gavinlyonsrepo/Cap_meter_arduino/docs/eagle/cap_meter.sch

## EAGLE design docs/eagle/cap_meter.sch (2019-02-24)

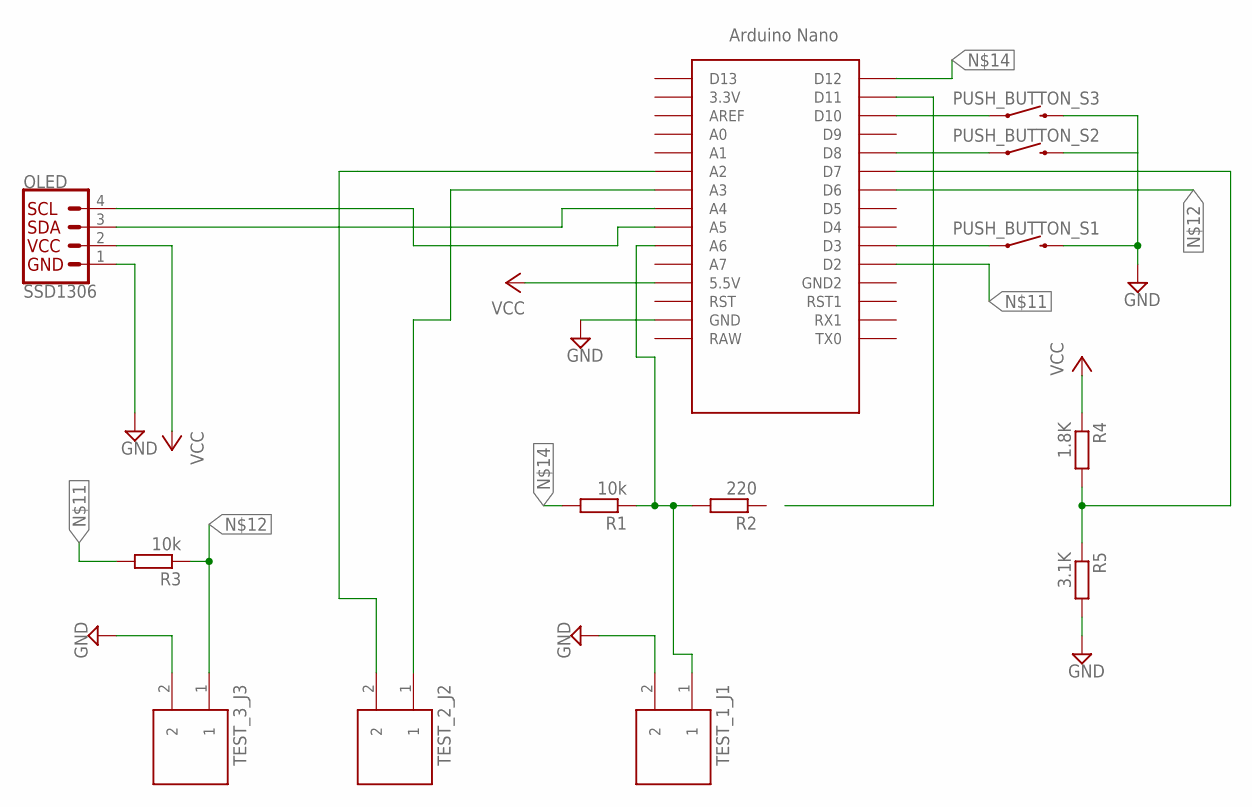
[picture p8: schematic cap_meter.sch]

Parts:
OLED: SSD1306; 1X04
PUSH_BUTTON_S1, PUSH_BUTTON_S2, PUSH_BUTTON_S3: MOMENTARY-SWITCH-SPST-PTH-6.0MM-KIT; TACTILE_SWITCH_PTH_6.0MM_KIT
R1, R3: 10k; R1210
R2: 220; R1210
R4: 1.8K; R1210
R5: 3.1K; R1210
TEST_1_J1, TEST_2_J2, TEST_3_J3: ED555/2DS
U$1: NANO

Connections:
GND: OLED.1, PUSH_BUTTON_S1.3 (2), PUSH_BUTTON_S2.3 (2), PUSH_BUTTON_S3.3 (2), R5.2, TEST_1_J1.2, TEST_3_J3.2, U$1.GND
unnamed: OLED.3, U$1.A4
unnamed: OLED.4, U$1.A5
unnamed: TEST_2_J2.1, U$1.A3
unnamed: PUSH_BUTTON_S2.1, U$1.D8
unnamed: TEST_2_J2.2, U$1.A2
unnamed: PUSH_BUTTON_S1.1, U$1.D3
unnamed: R1.1, R2.2, TEST_1_J1.1, U$1.A6
unnamed: PUSH_BUTTON_S3.1, U$1.D10
unnamed: R3.2, U$1.D2
unnamed: R3.1, TEST_3_J3.1, U$1.D6
unnamed: R4.2, R5.1, U$1.D7
unnamed: R1.2, U$1.D12
VCC: OLED.2, R4.1, U$1.5V (5.5V)
